ArsenShana/GPS-ES32/output/gps-presentation/assets/powerbank.png

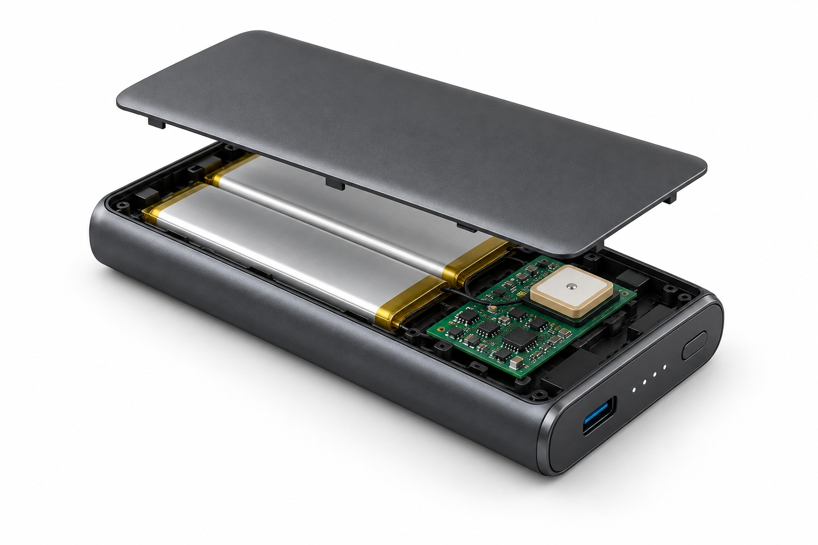
output/gps-presentation/assets/powerbank.png
