ArsenShana/GPS-ES32/output/gps-presentation-expanded/overview.jpg

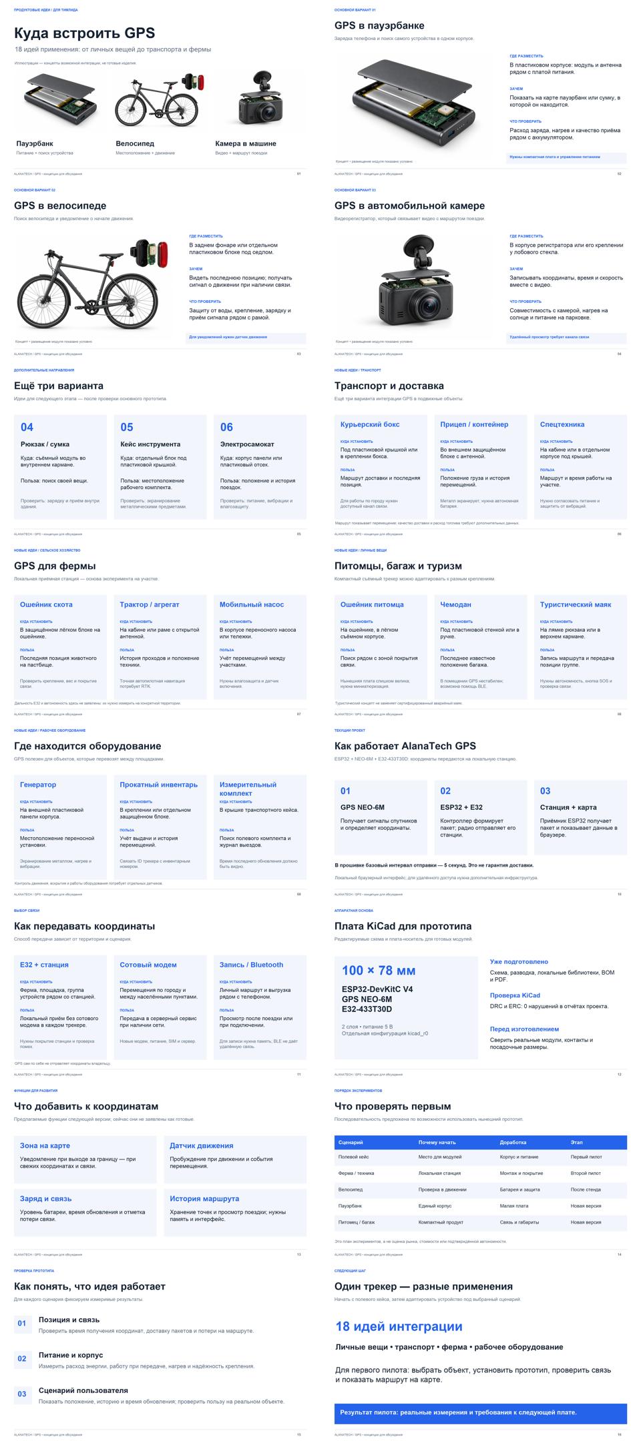
output/gps-presentation-expanded/overview.jpg
