ArsenShana/GPS-ES32/output/gps-presentation-expanded/preview-01.png

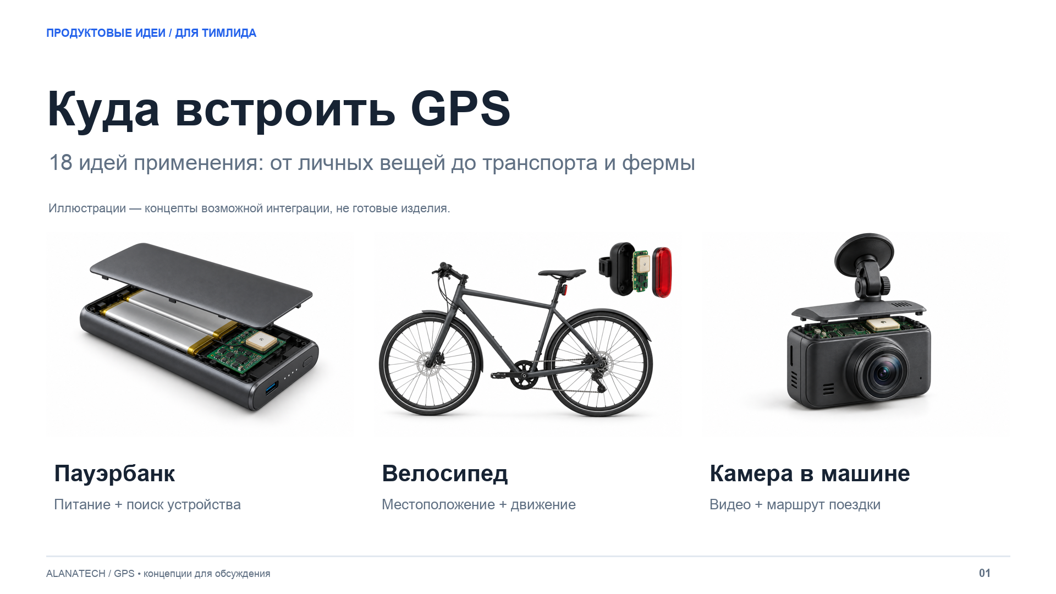
output/gps-presentation-expanded/preview-01.png
