ArsenShana/GPS-ES32/output/gps-presentation-expanded/preview-02.png

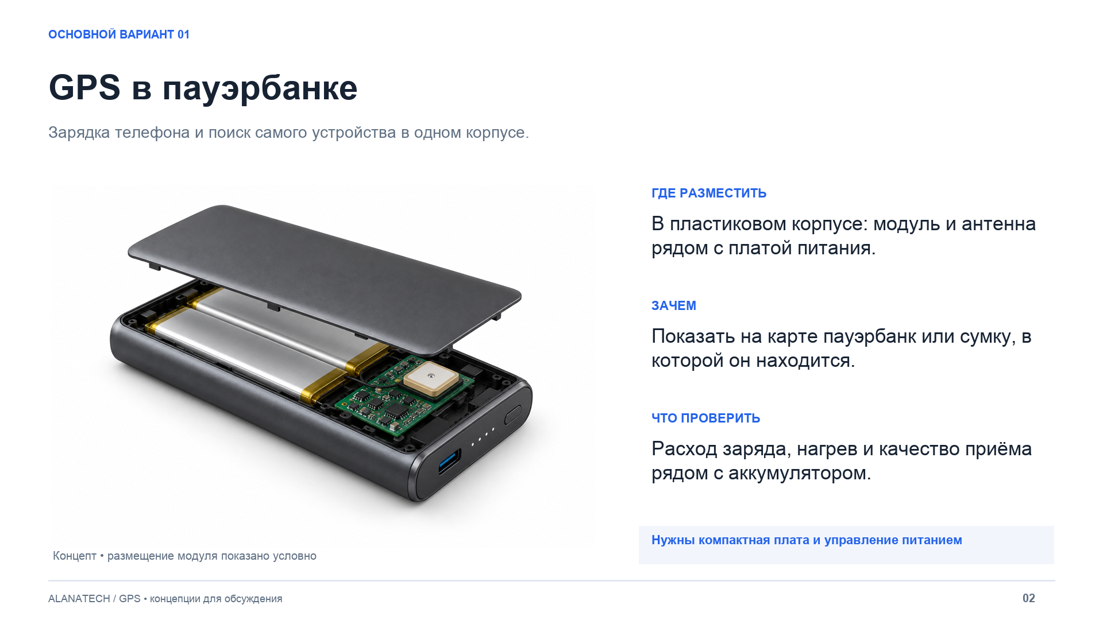
output/gps-presentation-expanded/preview-02.png
