ArsenShana/GPS-ES32/output/gps-presentation-expanded/preview-03.png

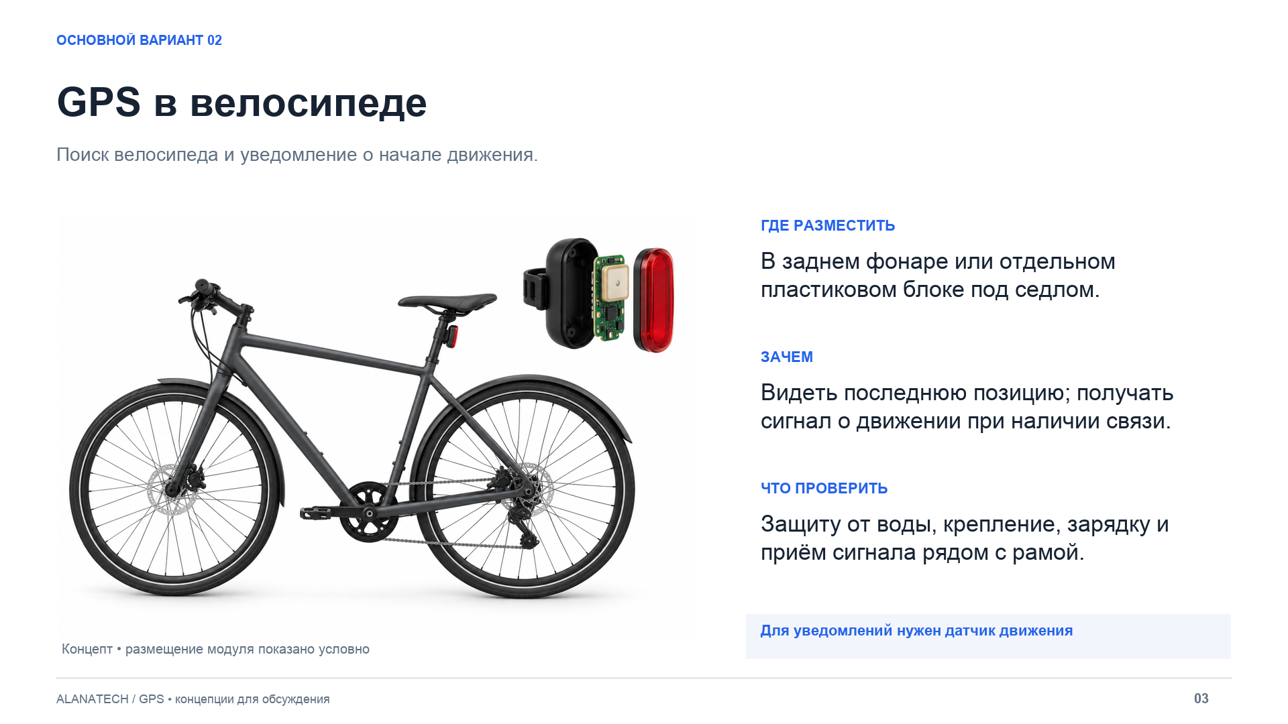
output/gps-presentation-expanded/preview-03.png
