ArsenShana/GPS-ES32/output/gps-presentation-expanded/preview-04.png

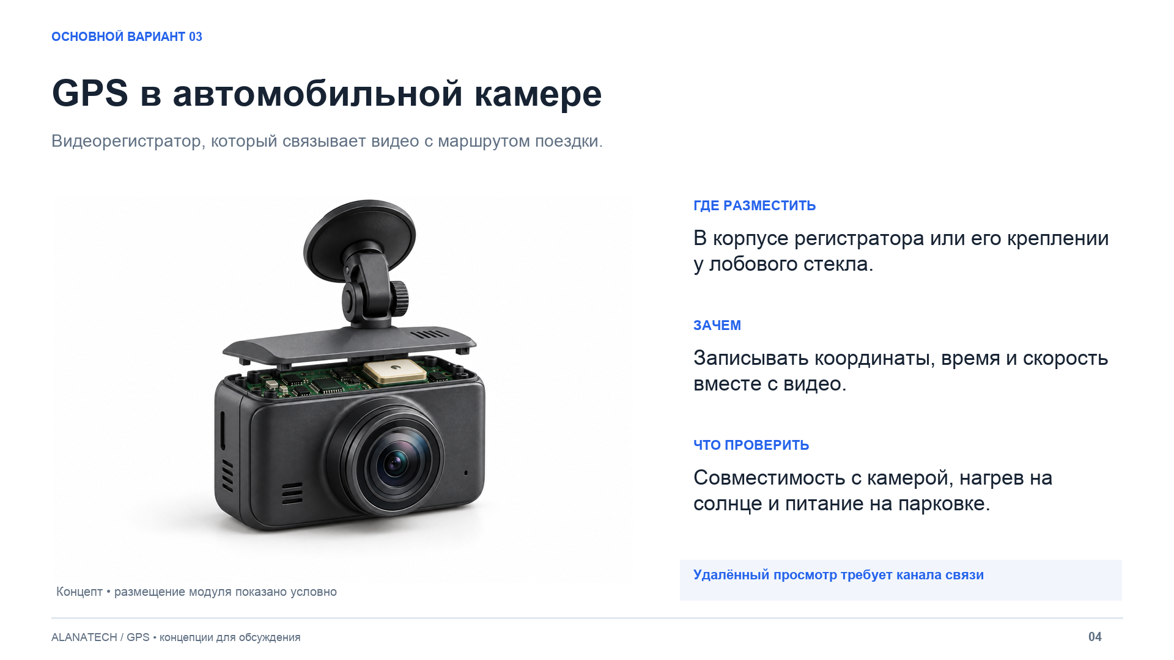
output/gps-presentation-expanded/preview-04.png
