ArsenShana/GPS-ES32/output/gps-presentation-expanded/preview-05.png

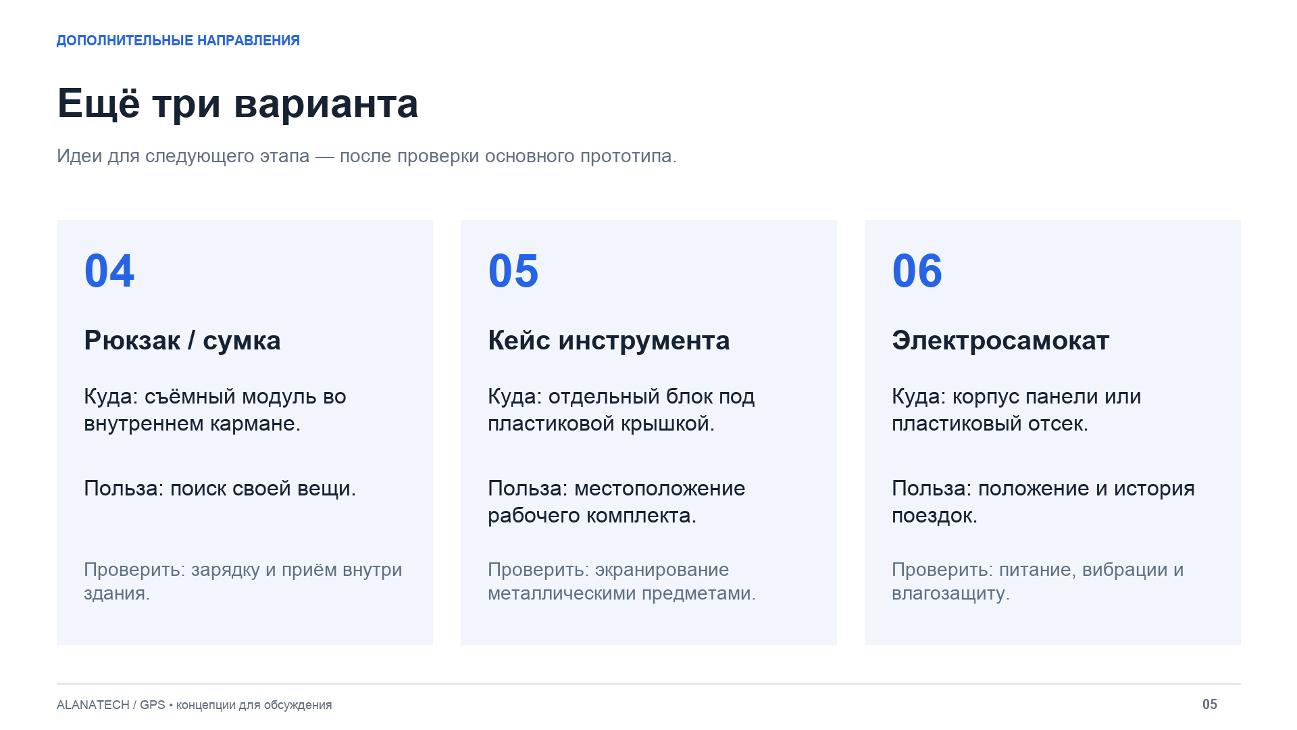
output/gps-presentation-expanded/preview-05.png
