ArsenShana/GPS-ES32/output/gps-presentation-expanded/preview-06.png

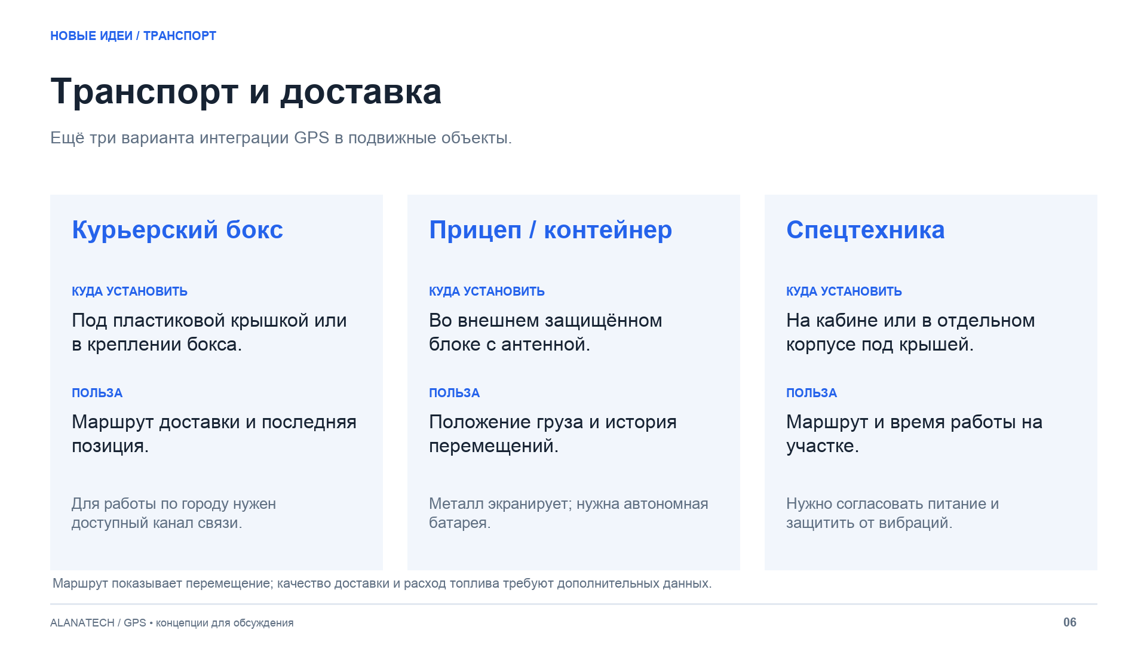
output/gps-presentation-expanded/preview-06.png
