ArsenShana/GPS-ES32/output/gps-presentation-expanded/preview-07.png

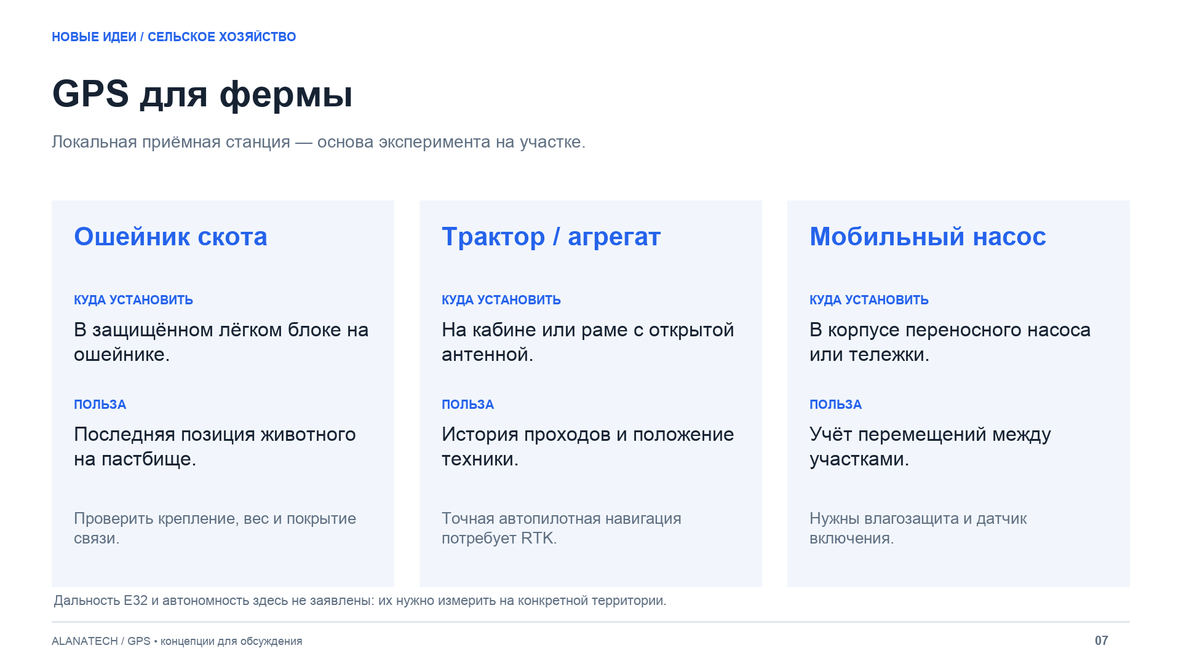
output/gps-presentation-expanded/preview-07.png
