ArsenShana/GPS-ES32/output/gps-presentation-expanded/preview-08.png

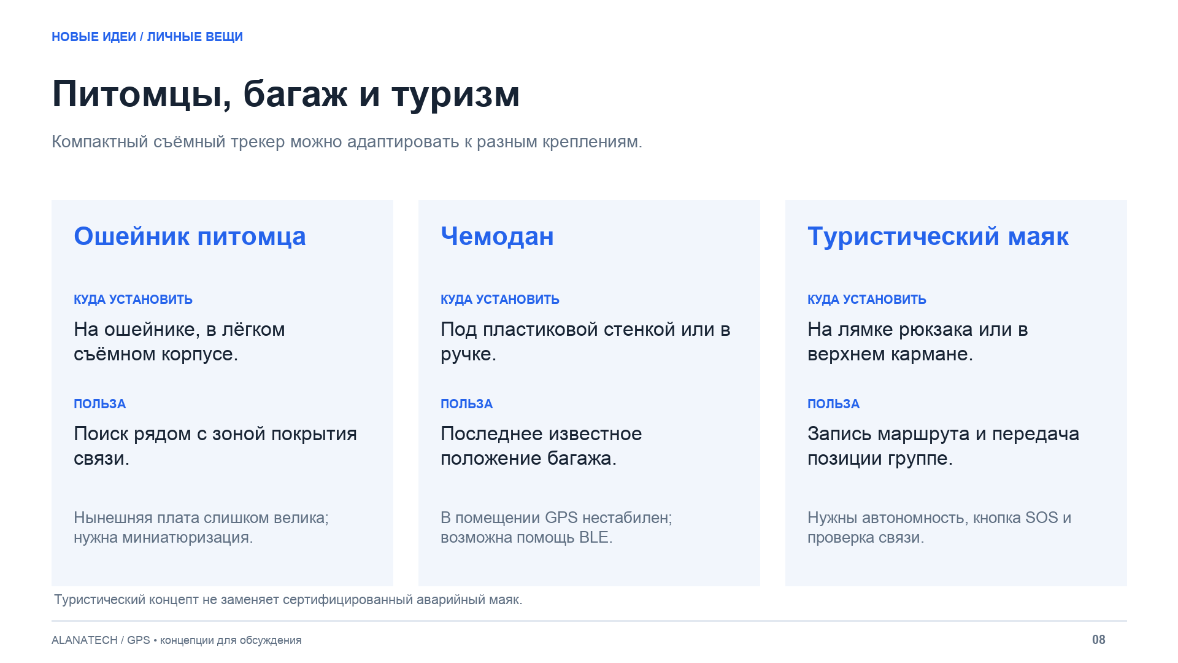
output/gps-presentation-expanded/preview-08.png
