ArsenShana/GPS-ES32/output/gps-presentation-expanded/preview-09.png

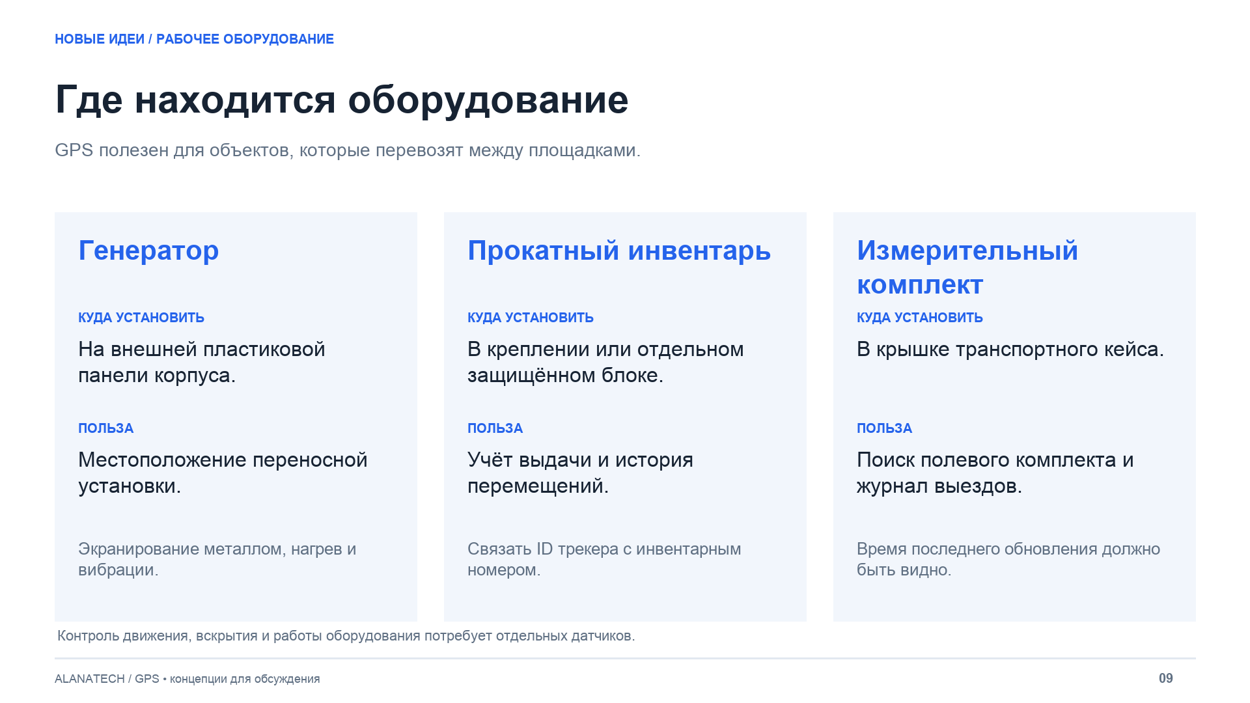
output/gps-presentation-expanded/preview-09.png
