ArsenShana/GPS-ES32/output/gps-presentation-expanded/preview-10.png

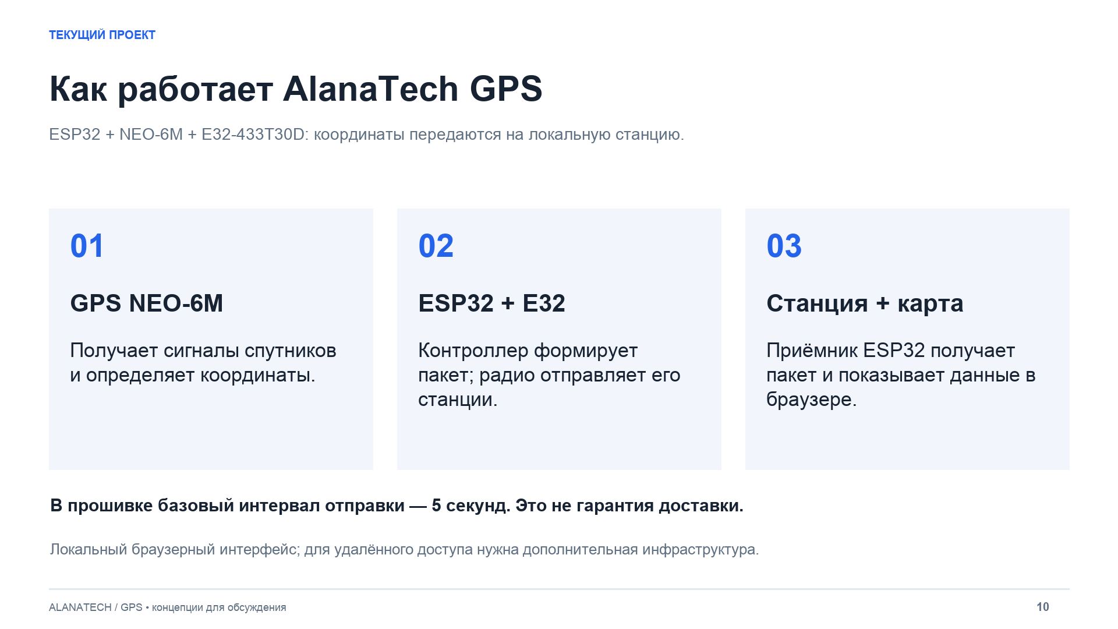
output/gps-presentation-expanded/preview-10.png
