ArsenShana/GPS-ES32/output/gps-presentation-expanded/preview-11.png

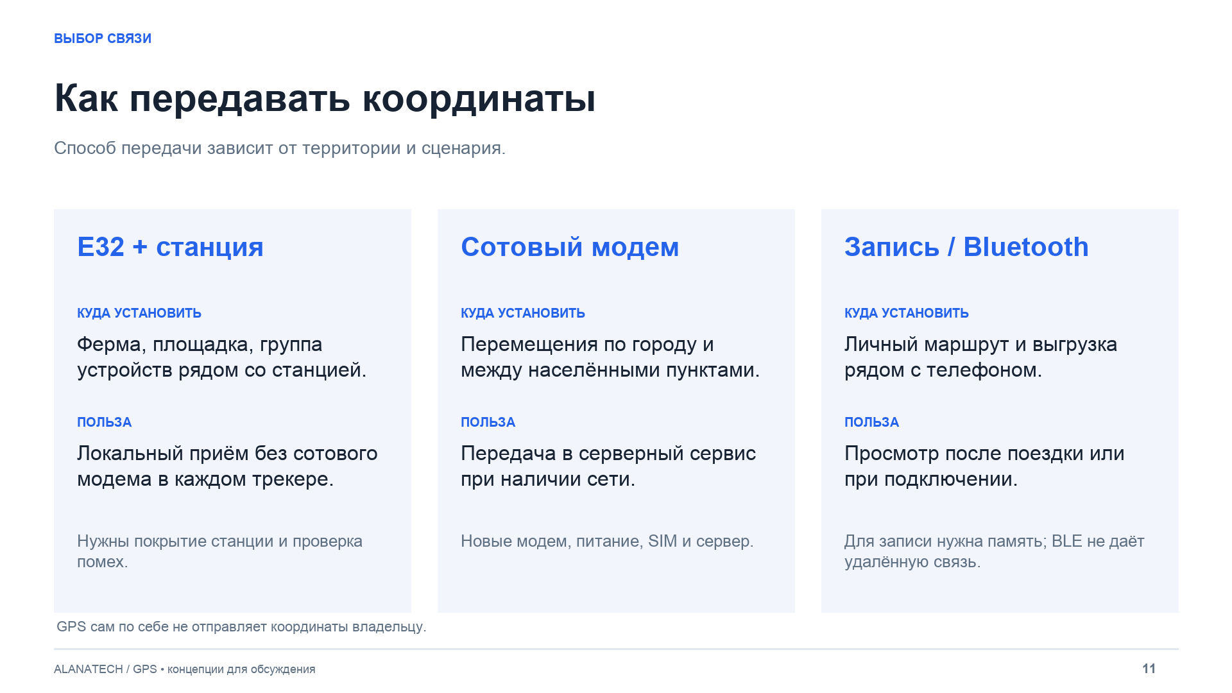
output/gps-presentation-expanded/preview-11.png
