ArsenShana/GPS-ES32/output/gps-presentation-expanded/preview-12.png

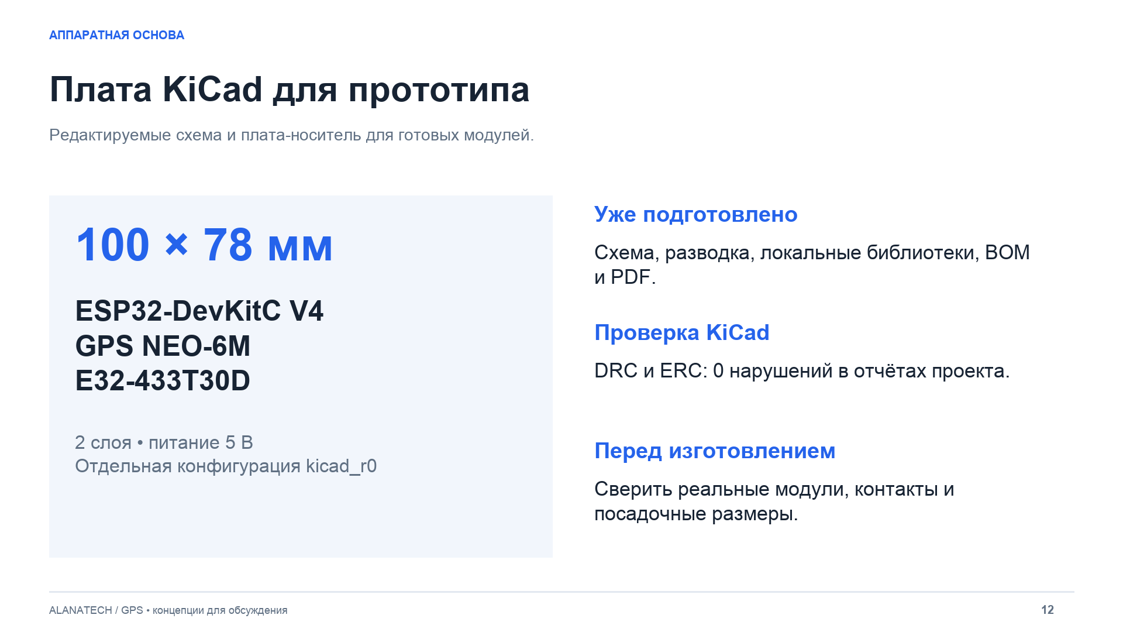
output/gps-presentation-expanded/preview-12.png
