ArsenShana/GPS-ES32/output/gps-presentation-expanded/preview-13.png

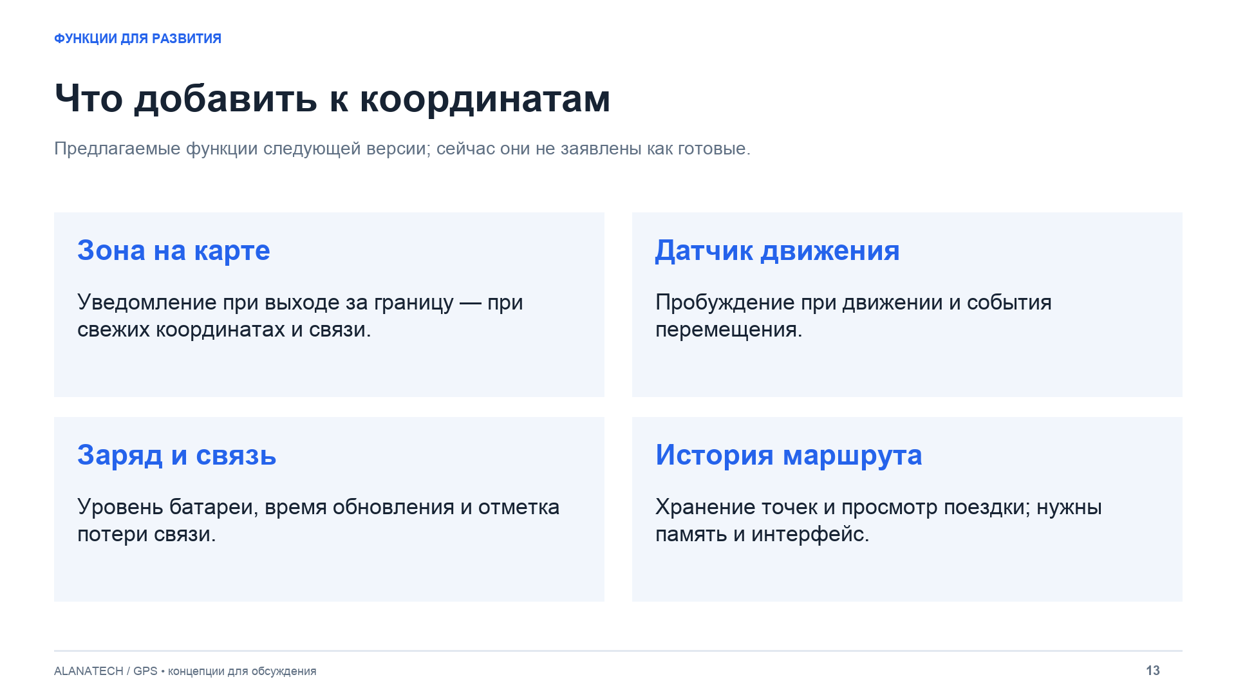
output/gps-presentation-expanded/preview-13.png
