ArsenShana/GPS-ES32/output/gps-presentation-expanded/preview-14.png

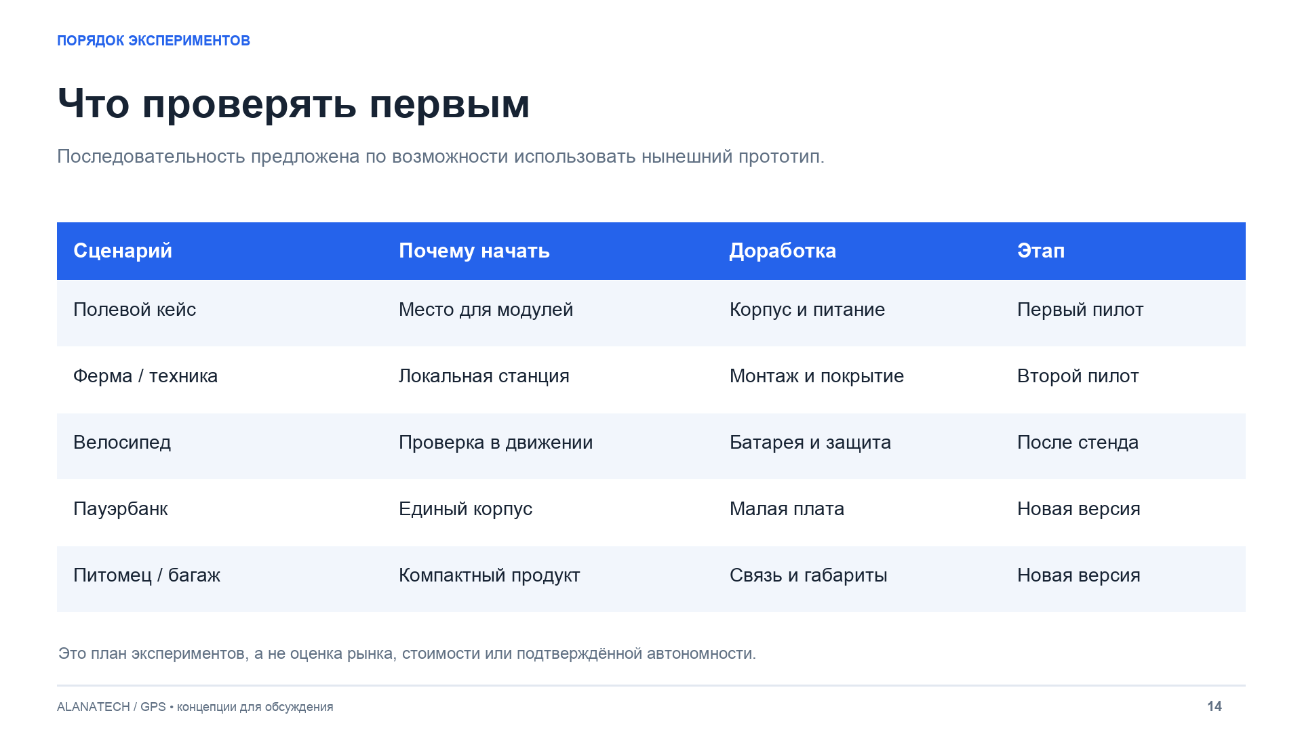
output/gps-presentation-expanded/preview-14.png
