ArsenShana/GPS-ES32/output/gps-presentation-expanded/preview-15.png

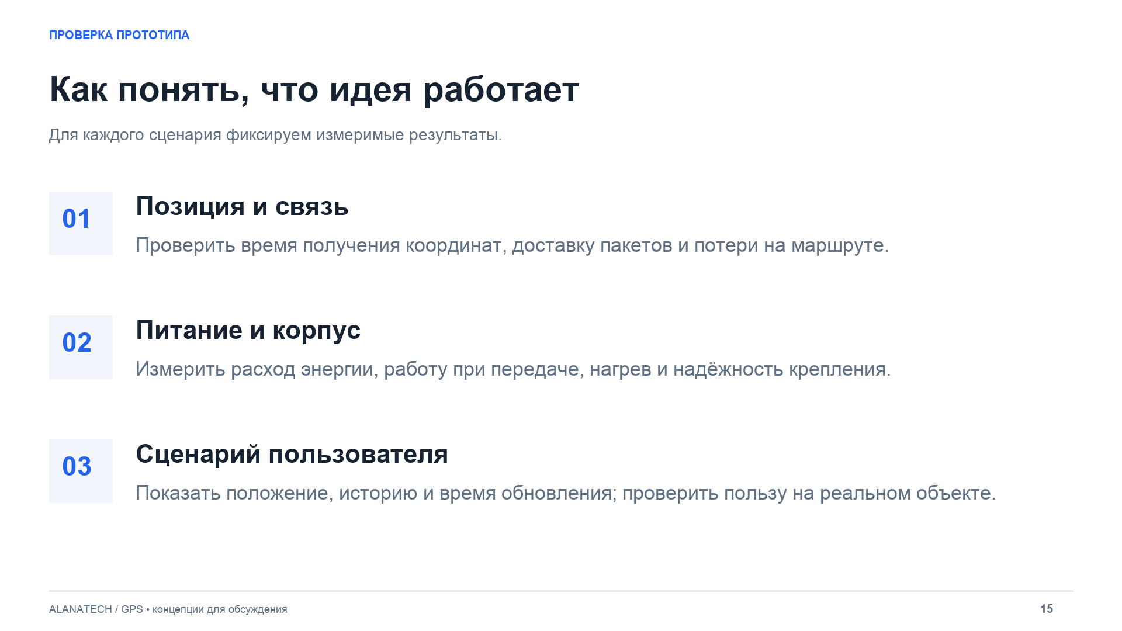
output/gps-presentation-expanded/preview-15.png
