ArsenShana/GPS-ES32/output/gps-presentation-expanded/preview-16.png

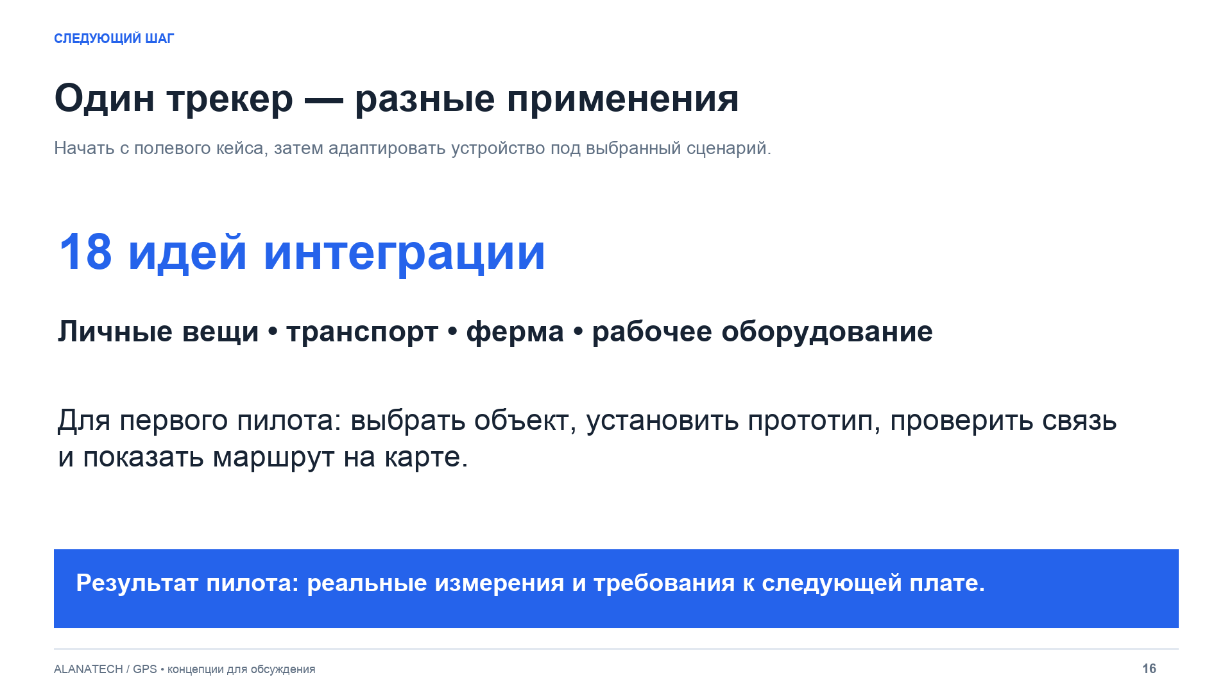
output/gps-presentation-expanded/preview-16.png
